MrZloHex/dc-ups-2ch/images/20260904_044944567.JPG

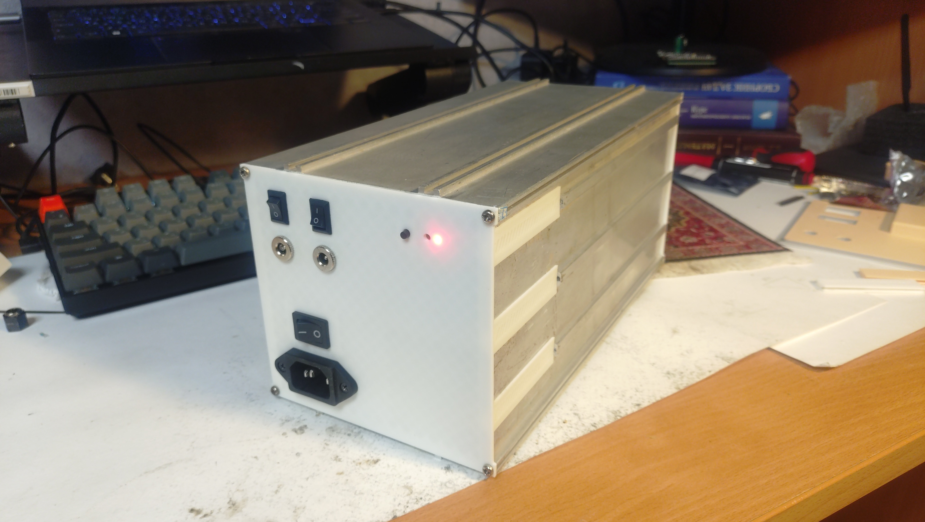
images/20260904_044944567.JPG
