MrZloHex/dc-ups-2ch/images/20260904_045149675.JPG

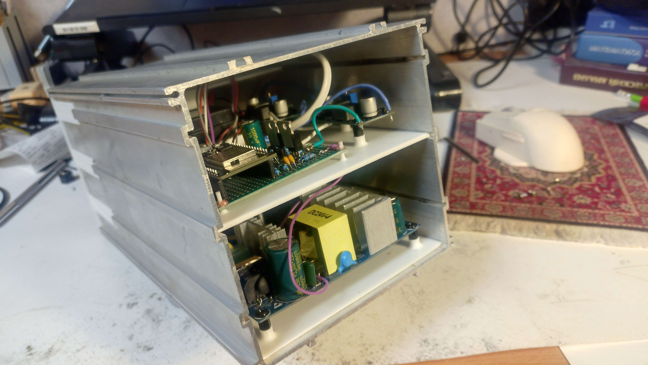
images/20260904_045149675.JPG
