MrZloHex/dc-ups-2ch/images/20260904_045319061.JPG

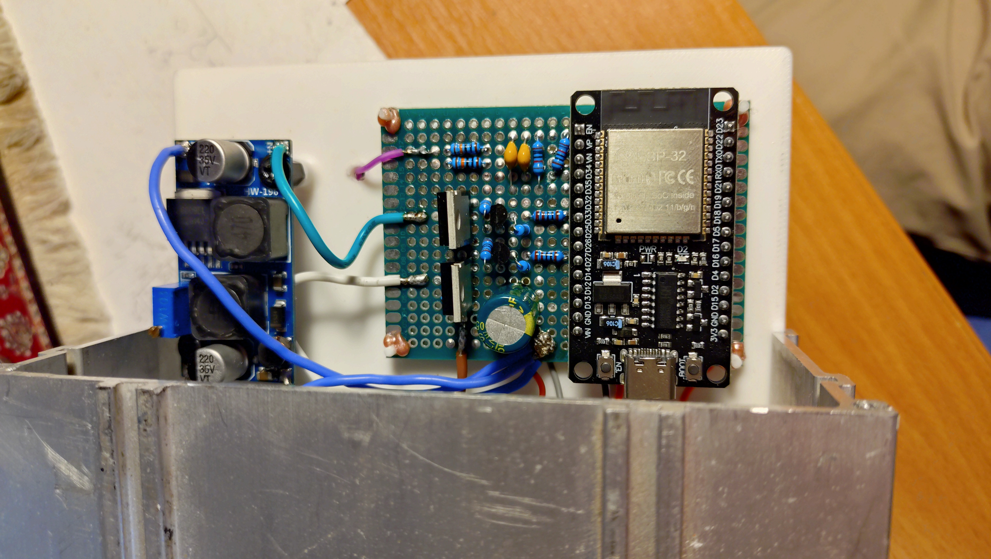
images/20260904_045319061.JPG
