MrZloHex/dc-ups-2ch/images/20260904_045514672.JPG

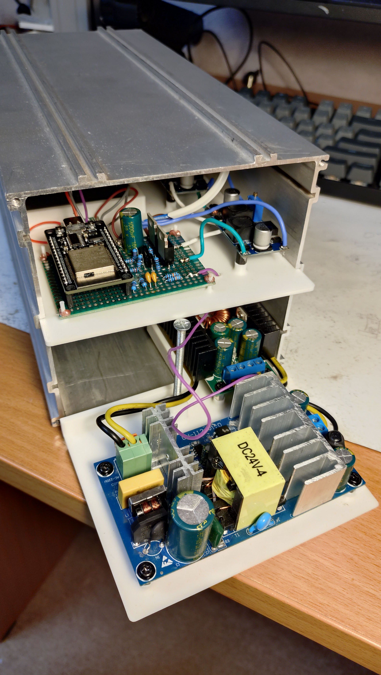
images/20260904_045514672.JPG
